keimschleuder/unkraut/Helpful/captures/1766066036624_q1.jpg

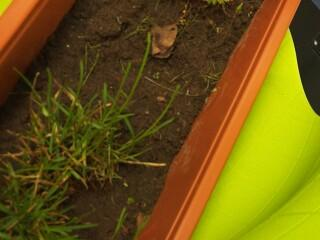
Helpful/captures/1766066036624_q1.jpg
