keimschleuder/unkraut/Dokumentation/schaltplan/schaltplan.kicad_sch

## KiCad design Dokumentation/schaltplan/schaltplan.kicad_sch (2025-12-29)

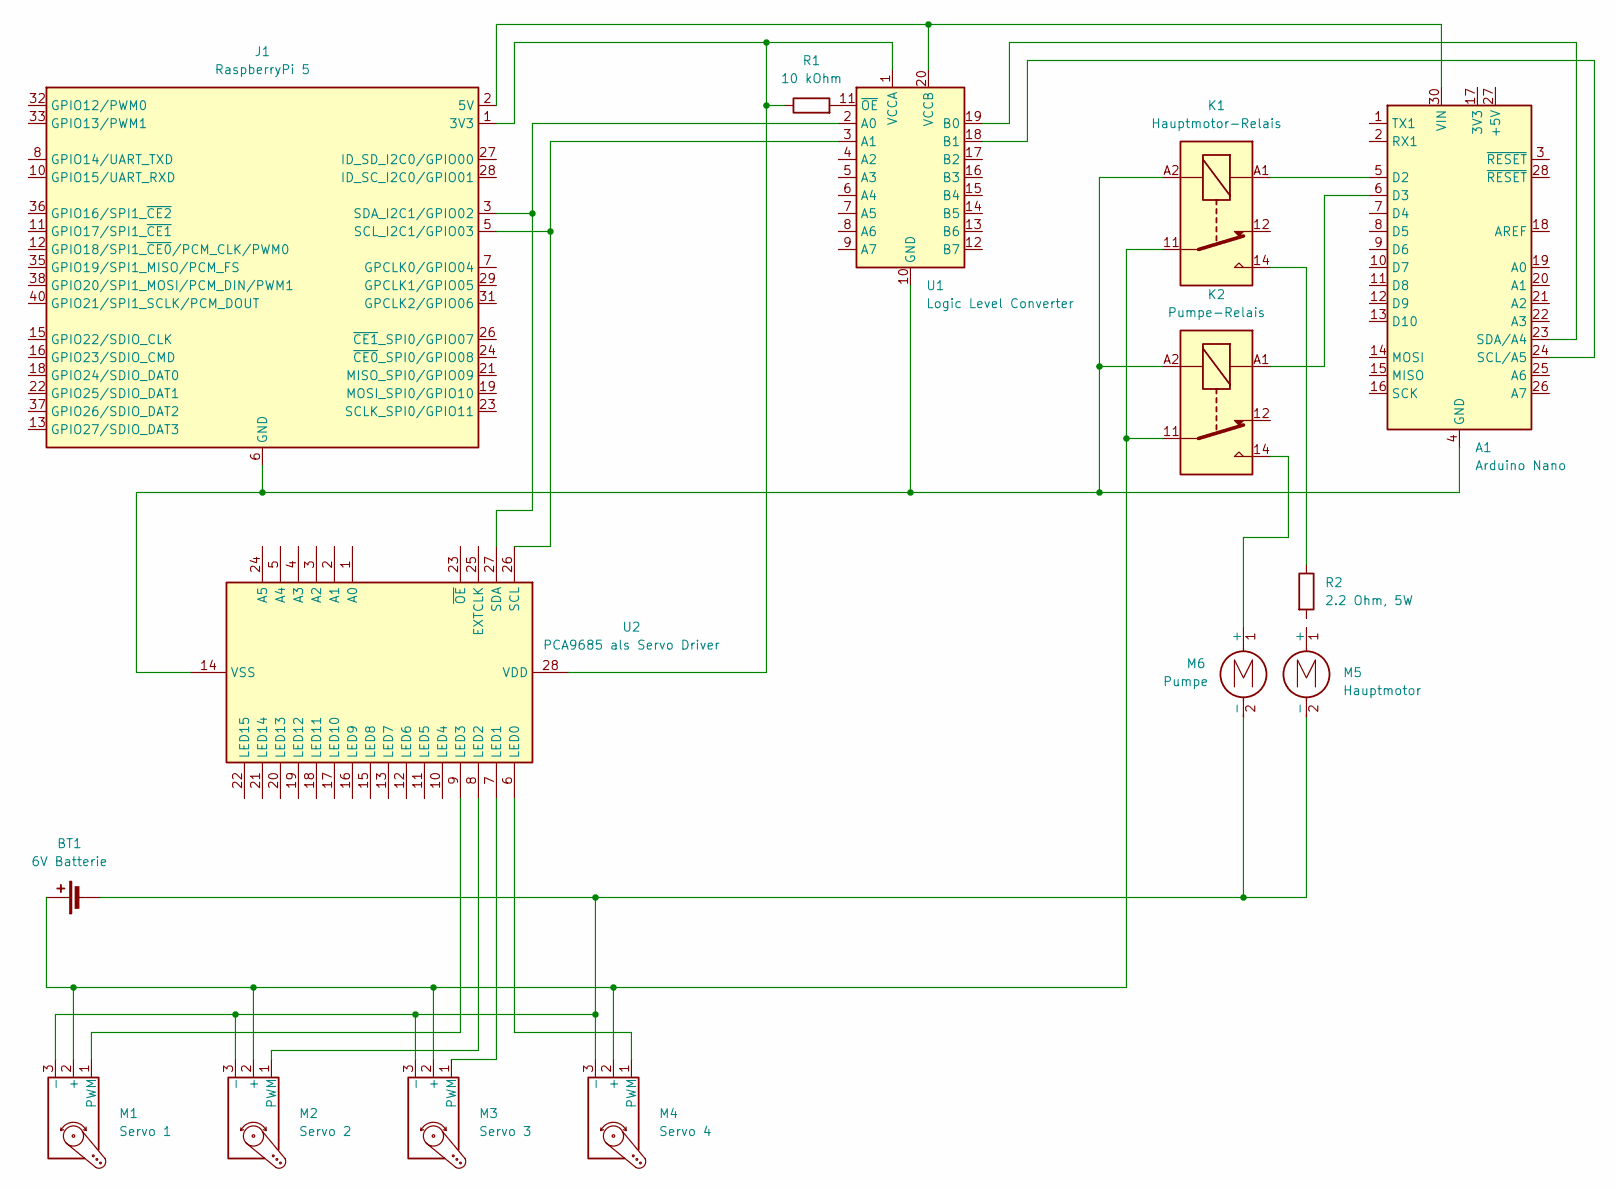
[picture p8: schematic schaltplan.kicad_sch]

Parts:
A1: Arduino Nano; Arduino_Nano
BT1: 6V Batterie
J1: RaspberryPi 5
K1: Hauptmotor-Relais; Relay_SPDT_Finder_40.41
K2: Pumpe-Relais; Relay_SPDT_Finder_40.41
M1: Servo 1
M2: Servo 2
M3: Servo 3
M4: Servo 4
M5: Hauptmotor
M6: Pumpe
R1: 10 kOhm
R2: 2.2 Ohm, 5W
U1: Logic Level Converter; WQFN-20-1EP_2.5x4.5mm_P0.5mm_EP1x2.9mm
U2: PCA9685 als Servo Driver; TSSOP-28_4.4x9.7mm_P0.65mm

Connections:
unnamed: A1.5 (D2), K1.A1
unnamed: A1.6 (D3), K2.A1
unnamed: A1.23 (SDA/A4), U1.19 (B0)
unnamed: A1.24 (SCL/A5), U1.18 (B1)
unnamed: A1.4 (GND), A1.29 (GND), J1.6 (GND), J1.9 (GND), J1.14 (GND), J1.20 (GND), J1.25 (GND), J1.30 (GND), J1.34 (GND), J1.39 (GND), K1.A2, K2.A2, U1.10 (GND), U2.14 (VSS)
unnamed: A1.30 (VIN), J1.2 (5V), J1.4 (5V), U1.20 (VCCB)
unnamed: BT1.1 (+), K1.11, K2.11, M1.2 (+), M2.2 (+), M3.2 (+), M4.2 (+)
unnamed: BT1.2 (-), M1.3 (-), M2.3 (-), M3.3 (-), M4.3 (-), M5.2 (-), M6.2 (-)
unnamed: J1.1 (3V3), J1.17 (3V3), R1.1, U1.1 (VCCA), U2.28 (VDD)
unnamed: J1.3 (SDA_I2C1/GPIO02), U1.2 (A0), U2.27 (SDA)
unnamed: J1.5 (SCL_I2C1/GPIO03), U1.3 (A1), U2.26 (SCL)
unnamed: K1.14, R2.1
unnamed: K2.14, M6.1 (+)
unnamed: M1.1 (PWM), U2.9 (LED3)
unnamed: M2.1 (PWM), U2.8 (LED2)
unnamed: M3.1 (PWM), U2.7 (LED1)
unnamed: M4.1 (PWM), U2.6 (LED0)
unnamed: R1.2, U1.11 (~OE)
