keimschleuder/unkraut/Helpful/camera.py

import time
import picamera2
import numpy as np
import cv2

with picamera2.Picamera2() as camera:
    camera.resolution = (320, 240)
    camera.framerate = 24
    time.sleep(2)
    image = np.empty((240 * 320 * 3,), dtype=np.uint8)
    camera.capture(image, 'bgr')
    image = image.reshape((240, 320, 3))
